auto-breakfast/-/doc/2018-11-21 (4).png

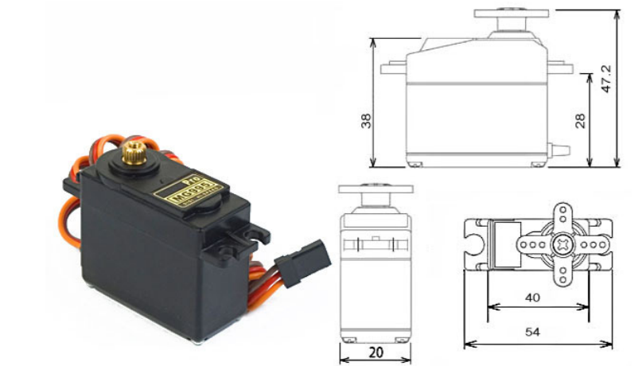
doc/2018-11-21 (4).png
