auto-breakfast/-/doc/2018-11-21 (5).png

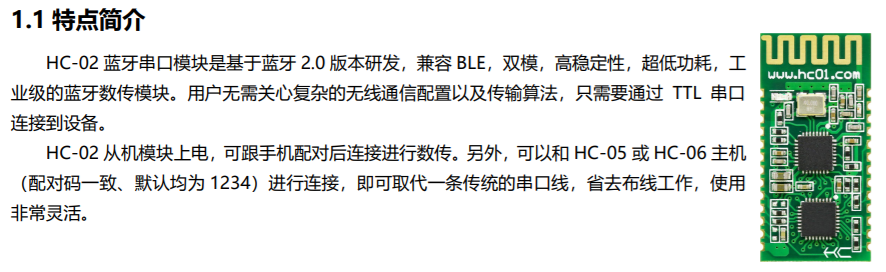
doc/2018-11-21 (5).png
