auto-breakfast/-/doc/2018-11-21 (6).png

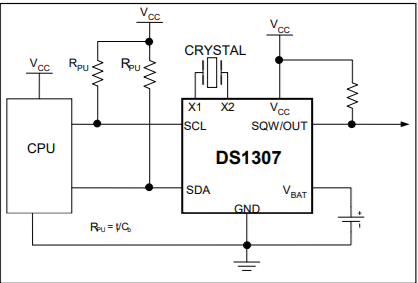
doc/2018-11-21 (6).png
