auto-breakfast/-/image/2019-01-11 (1).png

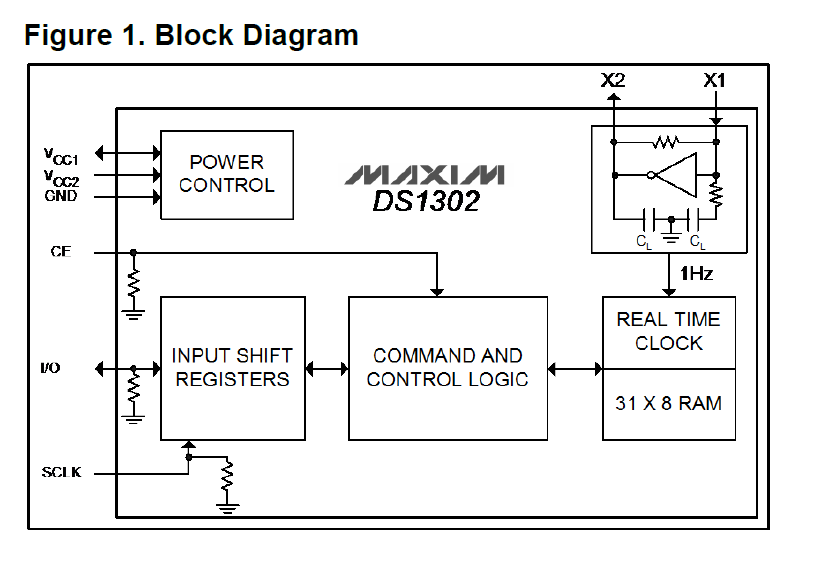
image/2019-01-11 (1).png
