auto-breakfast/-/src/defines.h

#ifndef _DEFINES_H
#define	_DEFINES_H

#include <xc.h> // include processor files - each processor file is guarded.  
typedef unsigned int u16;
typedef unsigned char u8;

typedef unsigned char bool;
#define true 1
#define false 0
#endif	/* XC_HEADER_TEMPLATE_H */
