auto-breakfast/-/src/mydelay.h

#ifndef MYDELAY_H
#define	MYDELAY_H  

/**
 *  ??:delay_ms(int ms) =>?????
 *  ?? ms:??????????int????
 *  ??:???? 
 *  <code>delay_ms(1000);</code>
 */
void delay_ms(int ms);
/**
 *  ??:delay_ms(int ms) =>?????
 *  ?? us:??????????int????
 */
void delay_us(int us);
void delayFor18Tcy(void);
#endif	
