auto-breakfast/-/src/uart.h

#ifndef _UART_H
#define _UART_H
#include <xc.h>
extern char uartdata[10]={0};
extern int lenght,TXFLAG;
extern int time[3]={0};

void initalUART(void);
void interrupt UART(void);
void writeuart(unsigned char *data);
void gettime(void);


#endif
